nehenemilabs/SkinnerDuino-shield/gerber/pdf/SkinnerDuino_05b_etch_silk_bottom.pdf

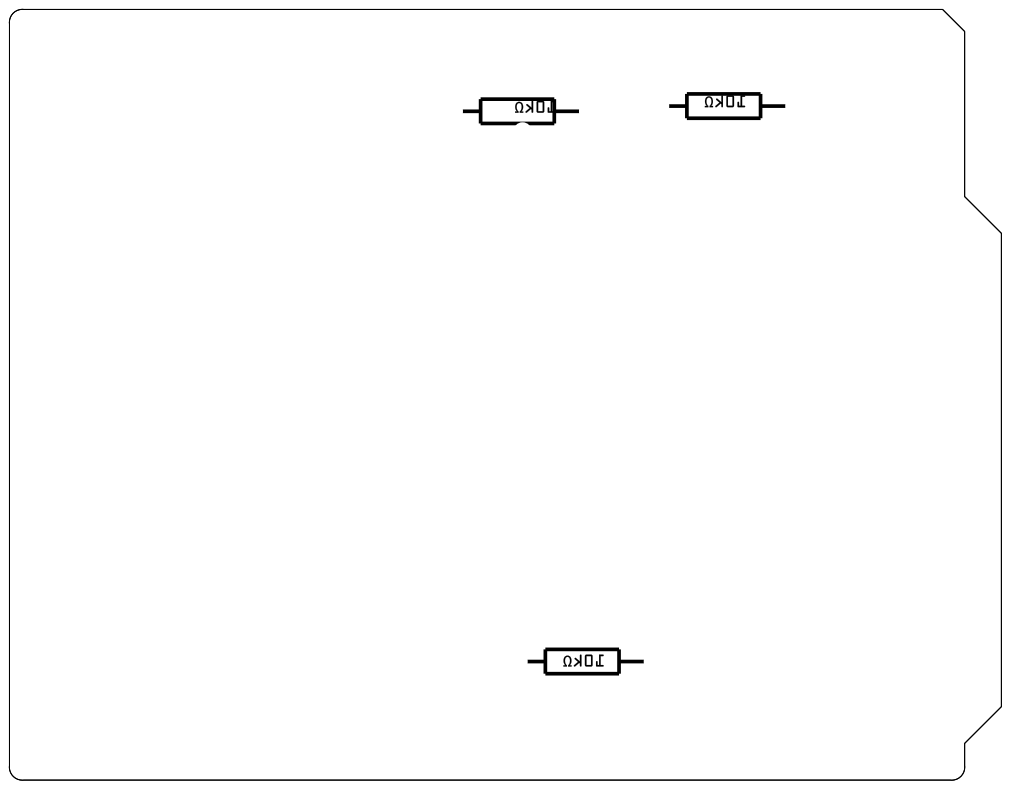
[picture p13: page 1]
