nehenemilabs/SkinnerDuino-shield/gerber/pdf/SkinnerDuino_05b_etch_silk_bottom_mirror.pdf

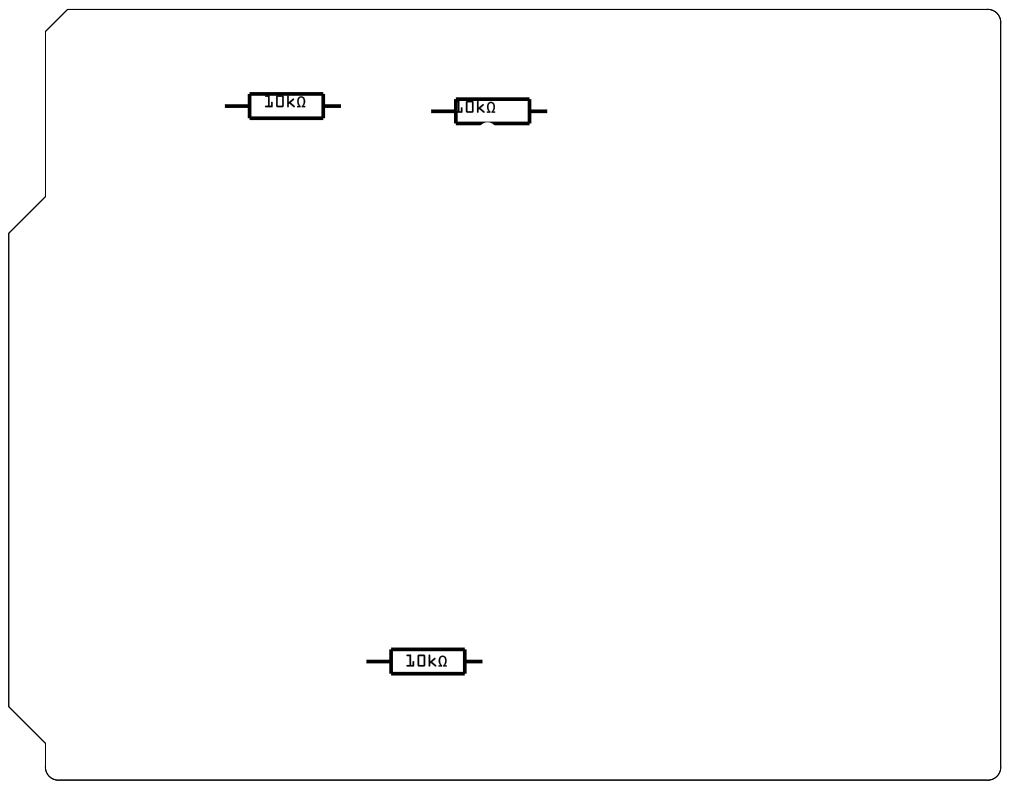
[picture p14: page 1]
