nehenemilabs/SkinnerDuino-shield/gerber/pdf/SkinnerDuino_05b_etch_silk_top.pdf

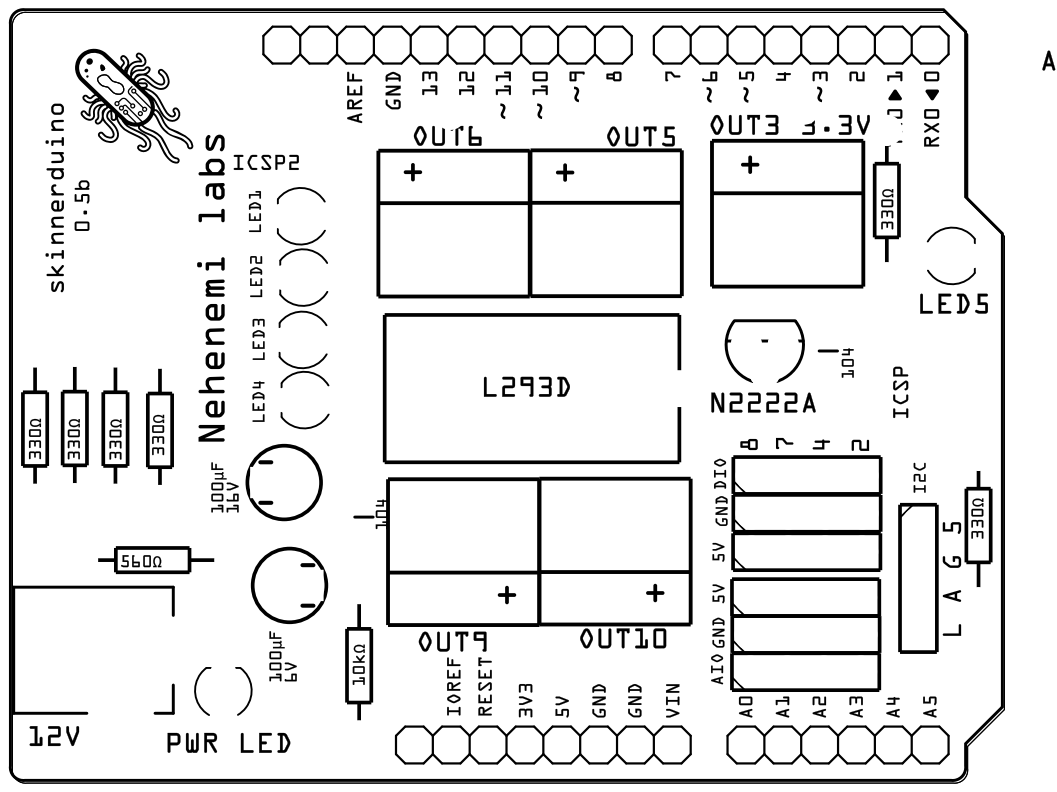
[picture p15: page 1]
