nehenemilabs/SkinnerDuino-shield/gerber/pdf/SkinnerDuino_05b_etch_silk_top_mirror.pdf

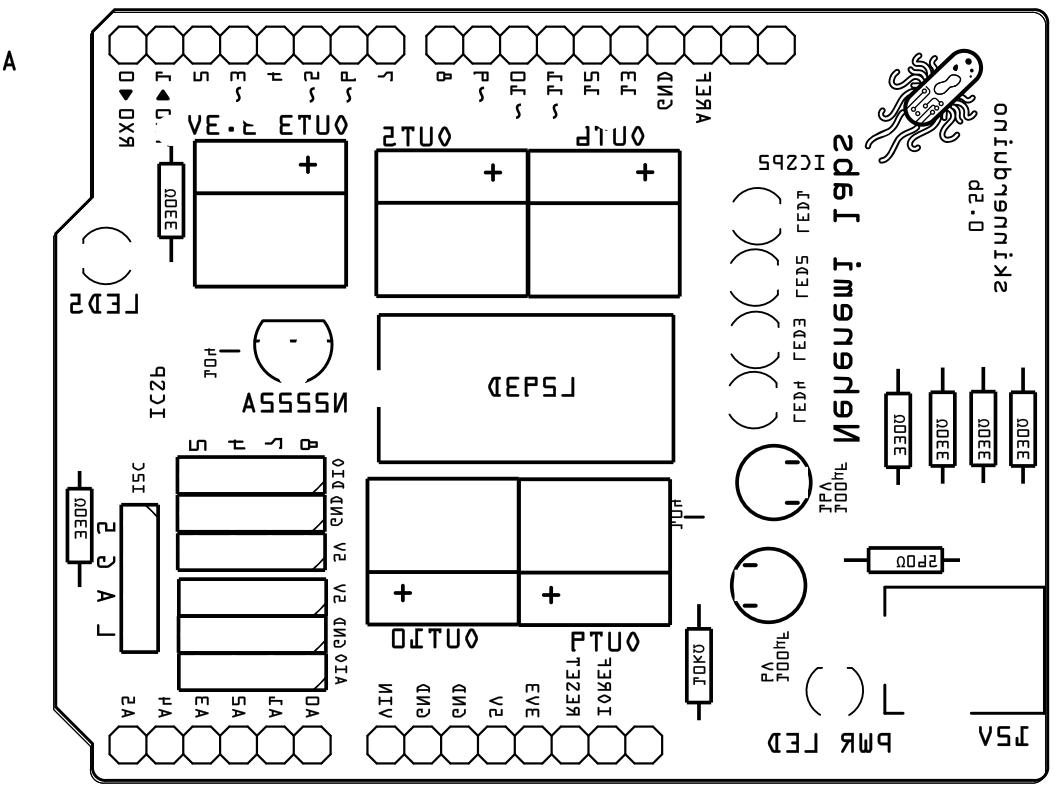
[picture p16: page 1]
